Alan-GIRAUDON/ESPCameleon/ESPCameleon.kicad_sch

## KiCad design ESPCameleon.kicad_sch (2024-11-30)

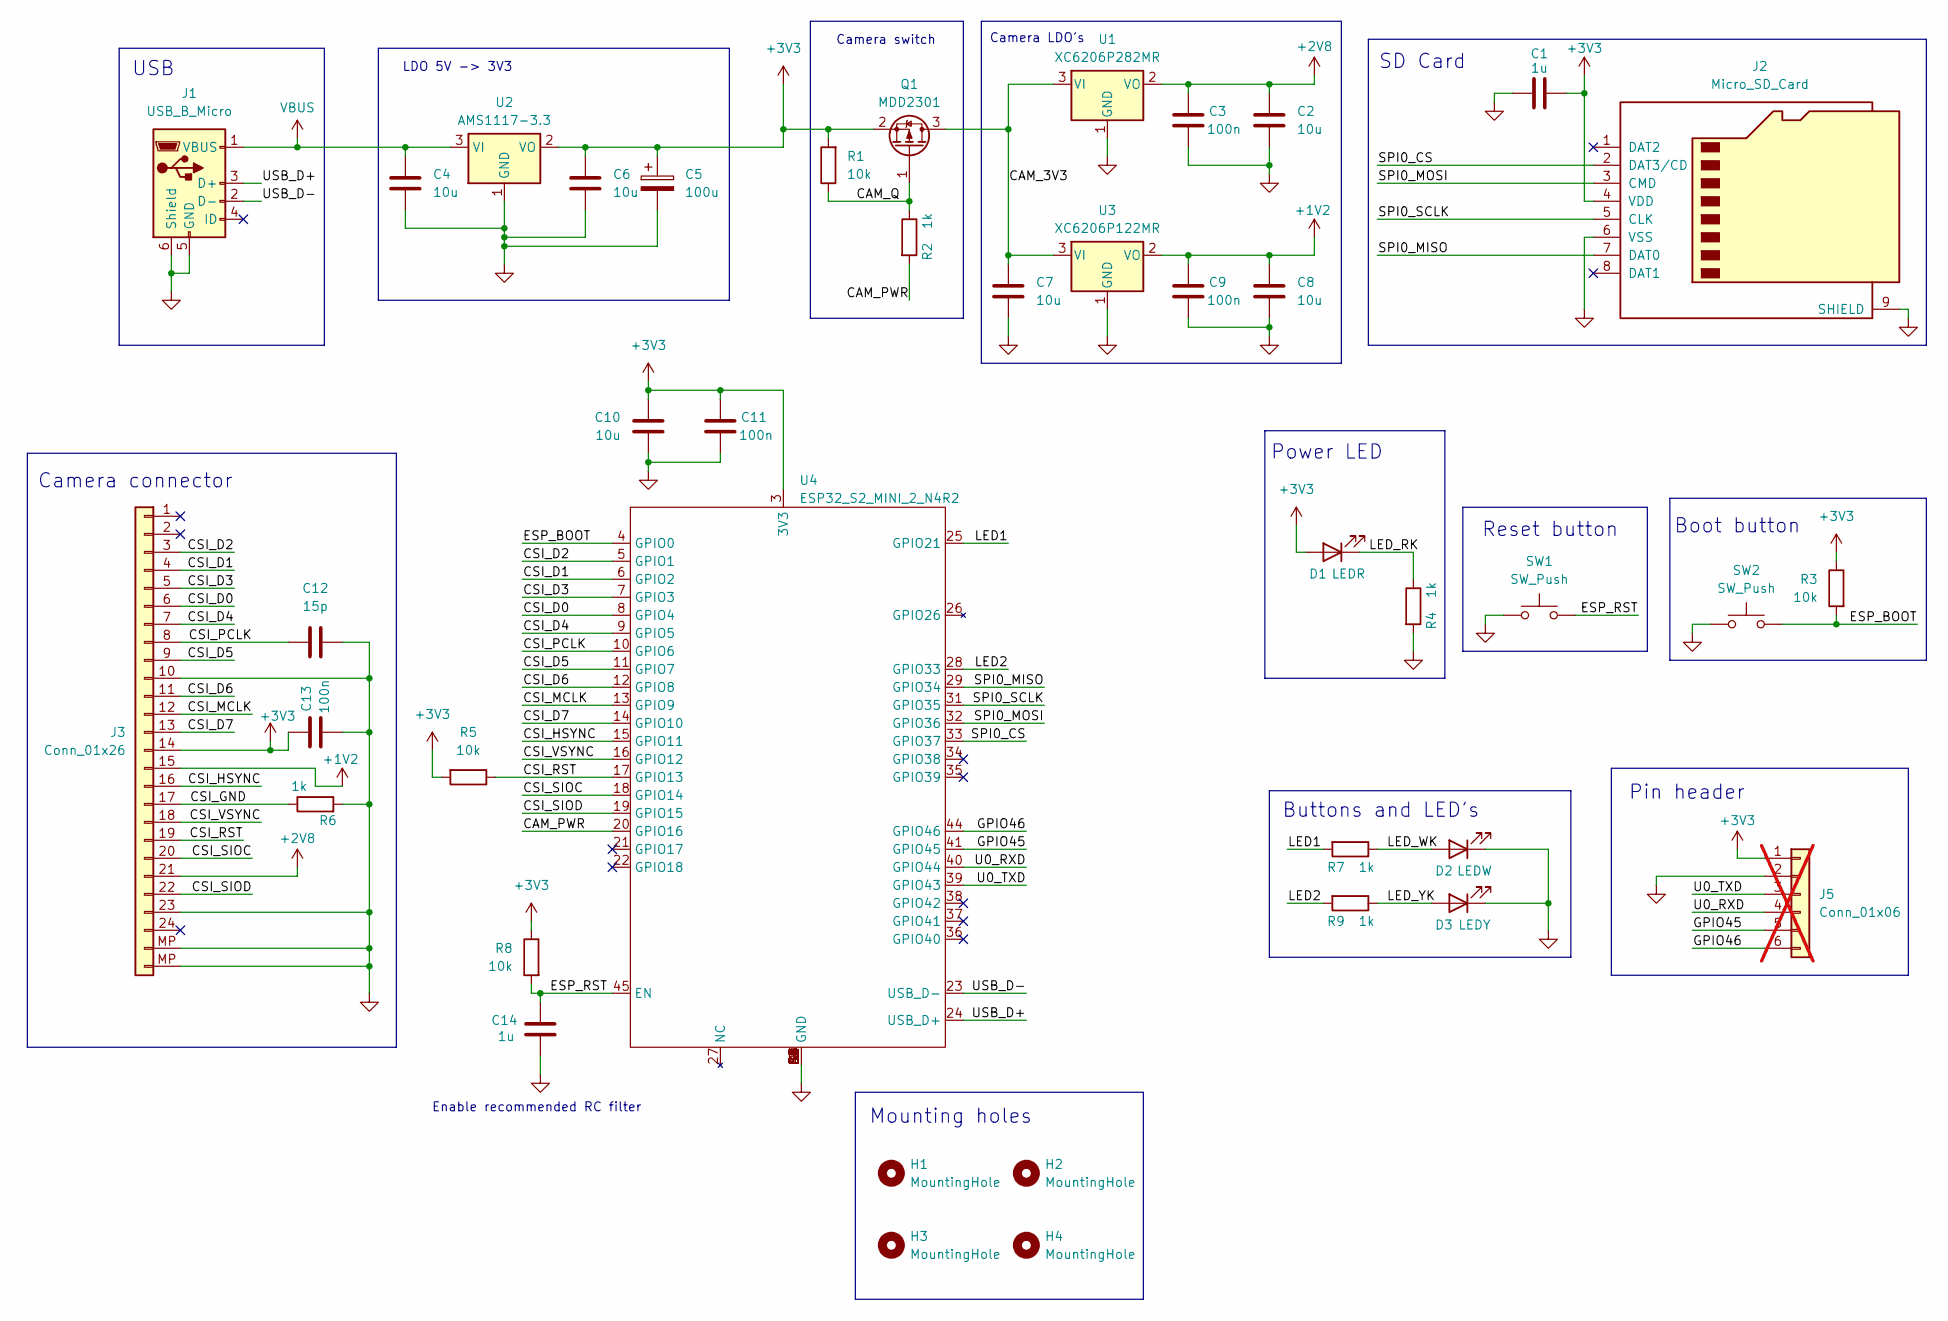
[picture p13: schematic ESPCameleon.kicad_sch]

Parts:
C1, C14: 1u; C_0603_1608Metric; LCSC Part # C15849
C2, C4, C6, C7, C8, C10: 10u; C_0402_1005Metric; LCSC Part # C15525
C3, C9, C11, C13: 100n; C_0402_1005Metric; LCSC Part # C307331
C5: 100u; CP_EIA-3528-21_Kemet-B; LCSC Part # C16133
C12: 15p; C_0402_1005Metric; LCSC Part # C1548
D1: LEDR; LED_0603_1608Metric; LCSC Part # C2286
D2: LEDW; LED_0603_1608Metric; LCSC Part # C2290
D3: LEDY; LED_0603_1608Metric; LCSC Part # C72038
H1, H2, H3, H4: MountingHole; MountingHole_2.2mm_M2; LCSC Part # X
J1: USB_B_Micro; USB_Micro-B_XKB_U254-051T-4BH83-F1S; LCSC Part # C393940
J2: Micro_SD_Card; GCT_MEM2075-00-140-01-A; LCSC Part # C393941
J3: Conn_01x26; AFC01_S24FCA_00; LCSC Part # C262669
J5: Conn_01x06; PinHeader_1x06_P2.54mm_Vertical; LCSC Part # C6332199; not fitted
Q1: MDD2301; SOT-23; LCSC Part # C427391
R1, R3, R5, R8: 10k; R_0402_1005Metric; LCSC Part # C25744
R2, R4, R6, R7, R9: 1k; R_0402_1005Metric; LCSC Part # C11702
SW1, SW2: SW_Push; SW_Push_1P1T_NO_6x6mm_H9.5mm; LCSC Part # C5127964
U1: XC6206P282MR; SOT-23-3; LCSC Part # C5148690
U2: AMS1117-3.3; SOT-223-3_TabPin2; LCSC Part # C6186
U3: XC6206P122MR; SOT-23-3; LCSC Part # C2827649
U4: ESP32_S2_MINI_2_N4R2; ESP32-S2-MINI-2; LCSC Part # C3013908

Connections:
+1V2: C8.1, C9.2, J3.15, U3.2 (VO)
+2V8: C2.1, C3.2, J3.21, U1.2 (VO)
+3V3: C1.2, C5.1, C6.1, C10.1, C11.2, C13.2, D1.2 (A), J2.4 (VDD), J3.14, J5.1, Q1.2 (S), R1.2, R3.1, R5.2, R8.1, U2.2 (VO), U4.3 (3V3)
CAM_3V3: C7.1, Q1.3 (D), U1.3 (VI), U3.3 (VI)
CAM_PWR: R2.2, U4.20 (GPIO16)
CAM_Q: Q1.1 (G), R1.1, R2.1
CSI_D0: J3.6, U4.8 (GPIO4)
CSI_D1: J3.4, U4.6 (GPIO2)
CSI_D2: J3.3, U4.5 (GPIO1)
CSI_D3: J3.5, U4.7 (GPIO3)
CSI_D4: J3.7, U4.9 (GPIO5)
CSI_D5: J3.9, U4.11 (GPIO7)
CSI_D6: J3.11, U4.12 (GPIO8)
CSI_D7: J3.13, U4.14 (GPIO10)
CSI_GND: J3.17, R6.1
CSI_HSYNC: J3.16, U4.15 (GPIO11)
CSI_MCLK: J3.12, U4.13 (GPIO9)
CSI_PCLK: C12.1, J3.8, U4.10 (GPIO6)
CSI_RST: J3.19, R5.1, U4.17 (GPIO13)
CSI_SIOC: J3.20, U4.18 (GPIO14)
CSI_SIOD: J3.22, U4.19 (GPIO15)
CSI_VSYNC: J3.18, U4.16 (GPIO12)
ESP_BOOT: R3.2, SW2.2, U4.4 (GPIO0)
ESP_RST: C14.1, R8.2, SW1.2, U4.45 (EN)
GND: C1.1, C2.2, C3.1, C4.2, C5.2, C6.2, C7.2, C8.2, C9.1, C10.2, C11.1, C12.2, C13.1, C14.2, D2.1 (K), D3.1 (K), J1.5 (GND), J1.6 (Shield), J2.6 (VSS), J2.9 (SHIELD), J3.10, J3.23, J3.MP, J5.2, R4.2, R6.2, SW1.1, SW2.1, U1.1 (GND), U2.1 (GND), U3.1 (GND), U4.1 (GND), U4.2 (GND), U4.30 (GND), U4.42 (GND), U4.43 (GND), U4.46 (GND), U4.47 (GND), U4.48 (GND), U4.49 (GND), U4.50 (GND), U4.51 (GND), U4.52 (GND), U4.53 (GND), U4.54 (GND), U4.55 (GND), U4.56 (GND), U4.57 (GND), U4.58 (GND), U4.59 (GND), U4.60 (GND), U4.61 (GND), U4.62 (GND), U4.63 (GND), U4.64 (GND), U4.65 (GND)
GPIO45: J5.5, U4.41 (GPIO45)
GPIO46: J5.6, U4.44 (GPIO46)
LED1: R7.2, U4.25 (GPIO21)
LED2: R9.2, U4.28 (GPIO33)
LED_RK: D1.1 (K), R4.1
LED_WK: D2.2 (A), R7.1
LED_YK: D3.2 (A), R9.1
SPI0_CS: J2.2 (DAT3/CD), U4.33 (GPIO37)
SPI0_MISO: J2.7 (DAT0), U4.29 (GPIO34)
SPI0_MOSI: J2.3 (CMD), U4.32 (GPIO36)
SPI0_SCLK: J2.5 (CLK), U4.31 (GPIO35)
U0_RXD: J5.4, U4.40 (GPIO44)
U0_TXD: J5.3, U4.39 (GPIO43)
USB_D+: J1.3 (D+), U4.24 (GPIO20)
USB_D-: J1.2 (D-), U4.23 (GPIO19)
VBUS: C4.1, J1.1 (VBUS), U2.3 (VI)

Notes on the sheet:
SD Card
USB
Reset button
Enable recommended RC filter
Camera switch
Mounting holes
Boot button
Buttons and LED's
Pin header
LDO 5V -> 3V3
Camera connector
Power LED
Camera LDO's
